borpendy/DSpi/3D Files/Plate/topcover.stl

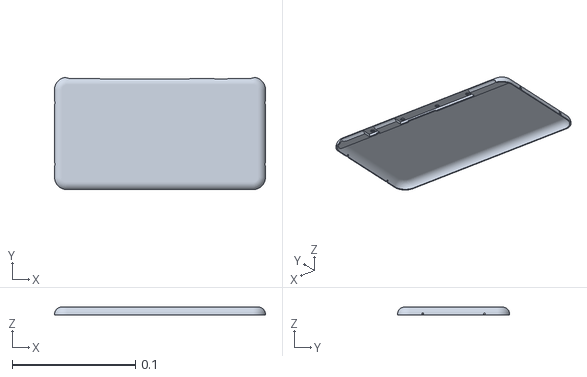
[picture p15: CAD file, 2025-08-22]
3D Files/Plate/topcover.stl
0.171 x 0.0909 x 0.0065
