borpendy/DSpi/3D Files/Buttons/Nosymbols/powerbutton.stl

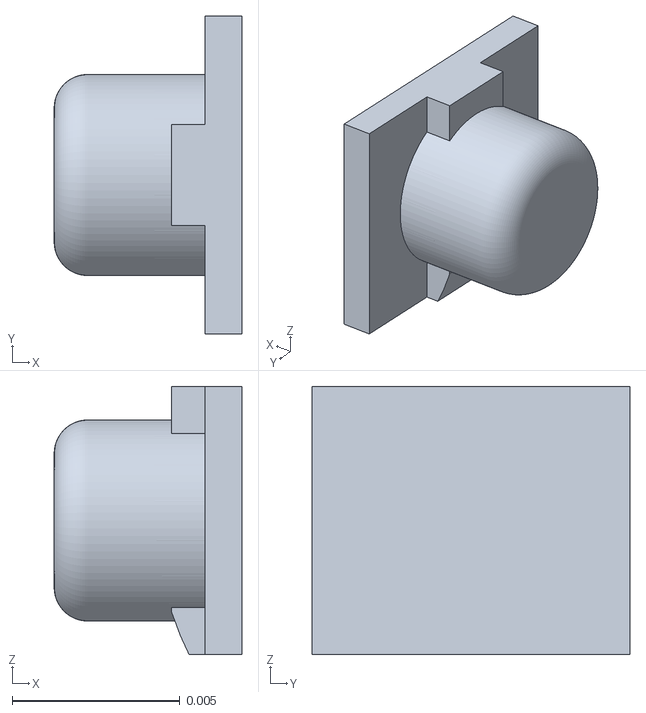
[picture p16: CAD file, 2025-08-22]
3D Files/Buttons/Nosymbols/powerbutton.stl
0.0056 x 0.00949 x 0.008
