borpendy/DSpi/3D Files/Buttons/Symbols/rt.stl

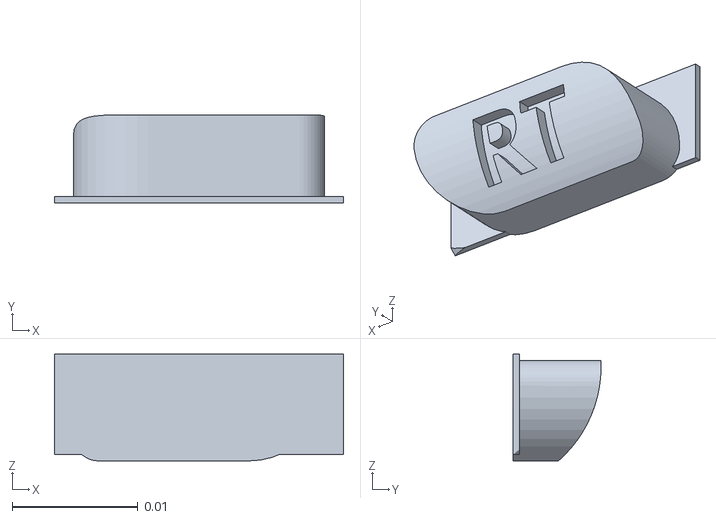
[picture p17: CAD file, 2025-08-22]
3D Files/Buttons/Symbols/rt.stl
0.023 x 0.00702 x 0.0085
