borpendy/DSpi/3D Files/Hinge/hinge-bottomleft.stl

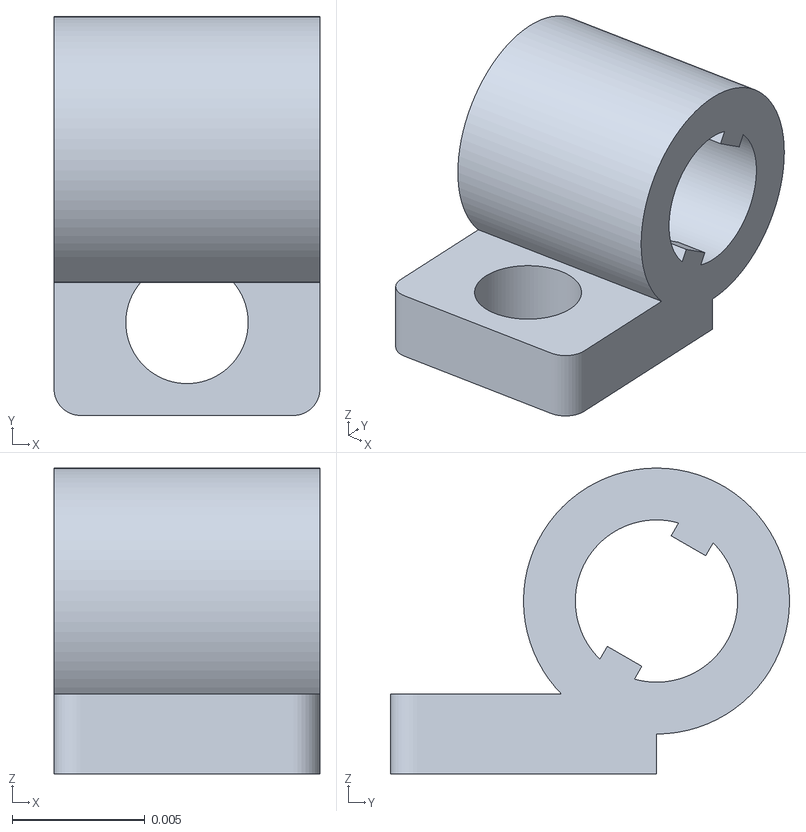
[picture p18: CAD file, 2025-08-22]
3D Files/Hinge/hinge-bottomleft.stl
0.01 x 0.015 x 0.0115
