borpendy/DSpi/3D Files/Misc/fanmount.stl

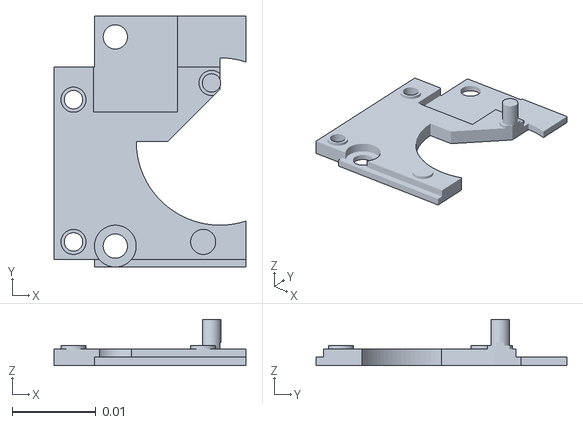
[picture p19: CAD file, 2025-08-22]
3D Files/Misc/fanmount.stl
0.0229 x 0.03 x 0.0055
