borpendy/DSpi/3D Files/Plate/lowerscreenmount-back.stl

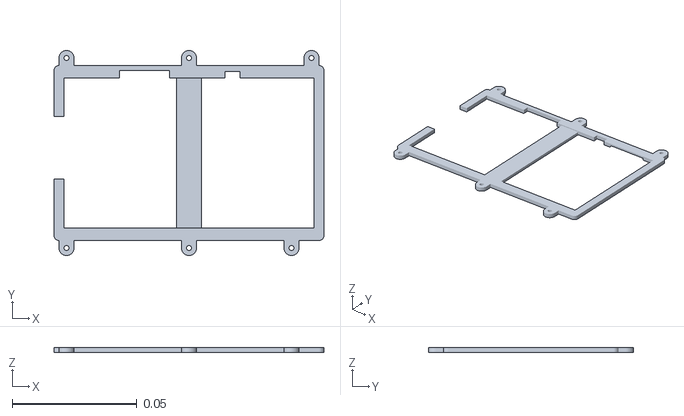
[picture p20: CAD file, 2025-08-22]
3D Files/Plate/lowerscreenmount-back.stl
0.108 x 0.082 x 0.002
