borpendy/DSpi/3D Files/Buttons/Symbols/rs.stl

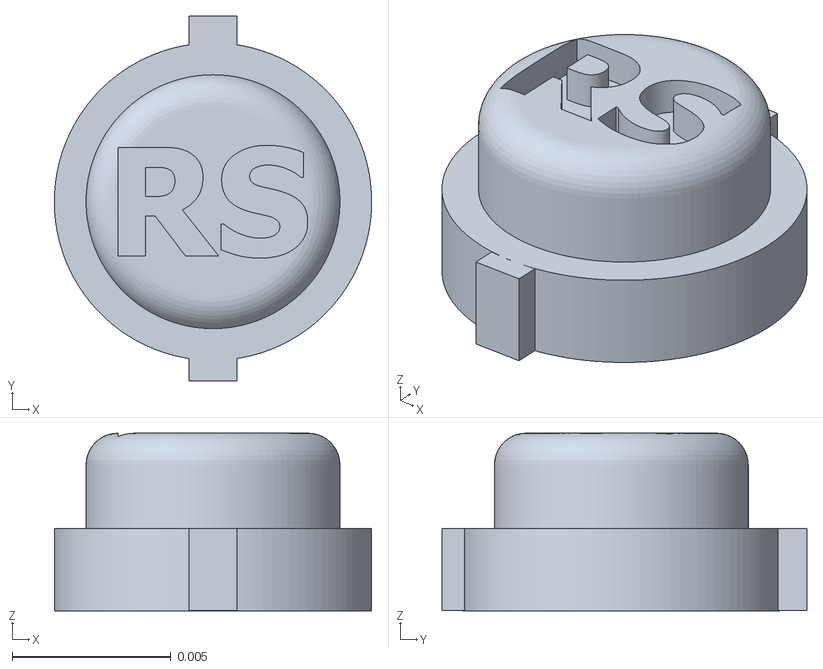
[picture p22: CAD file, 2025-08-22]
3D Files/Buttons/Symbols/rs.stl
0.01 x 0.0115 x 0.0056
