borpendy/DSpi/3D Files/Misc/batterymount.stl

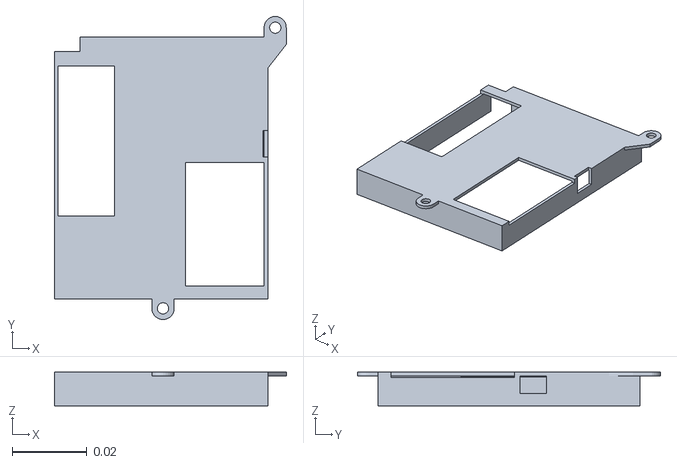
[picture p24: CAD file, 2025-08-22]
3D Files/Misc/batterymount.stl
0.062 x 0.081 x 0.009
