borpendy/DSpi/3D Files/Plate/lowerscreenmount.stl

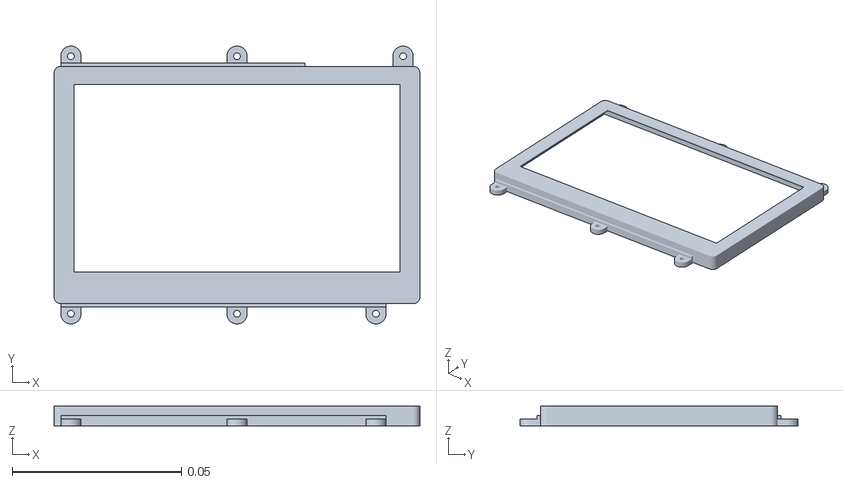
[picture p25: CAD file, 2025-08-22]
3D Files/Plate/lowerscreenmount.stl
0.108 x 0.082 x 0.0058
