borpendy/DSpi/3D Files/Hinge/topcover-l.stl

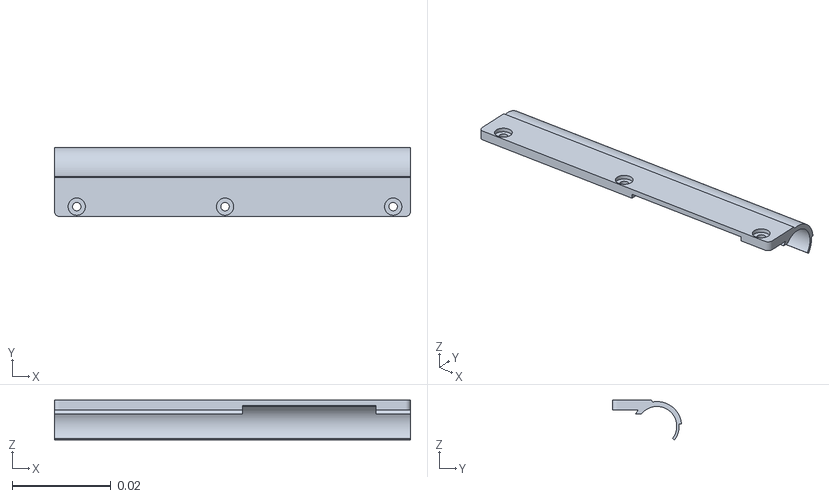
[picture p27: CAD file, 2025-08-22]
3D Files/Hinge/topcover-l.stl
0.072 x 0.014 x 0.00807
