borpendy/DSpi/3D Files/Plate/bottomplate.stl

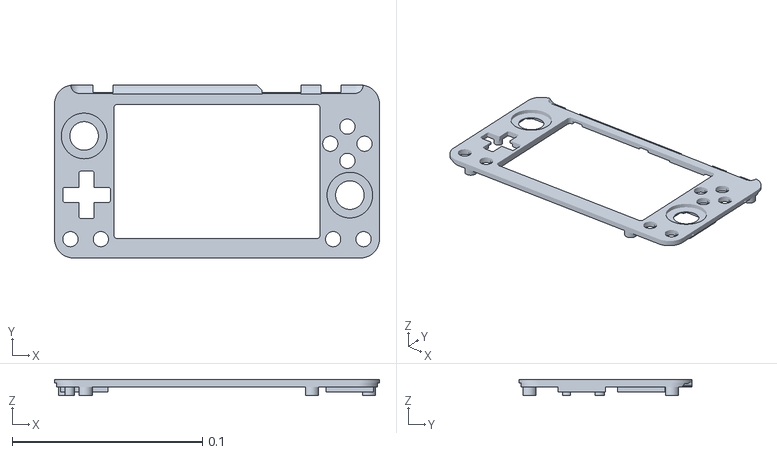
[picture p28: CAD file, 2025-08-22]
3D Files/Plate/bottomplate.stl
0.171 x 0.091 x 0.0085
