borpendy/DSpi/3D Files/Buttons/Symbols/x.stl

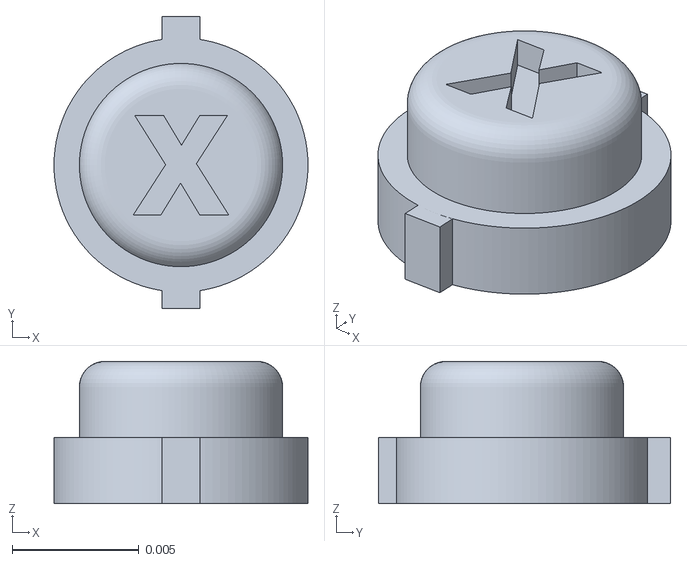
[picture p29: CAD file, 2025-08-22]
3D Files/Buttons/Symbols/x.stl
0.01 x 0.0115 x 0.0056
