borpendy/DSpi/3D Files/Hinge/hinge-topleft.stl

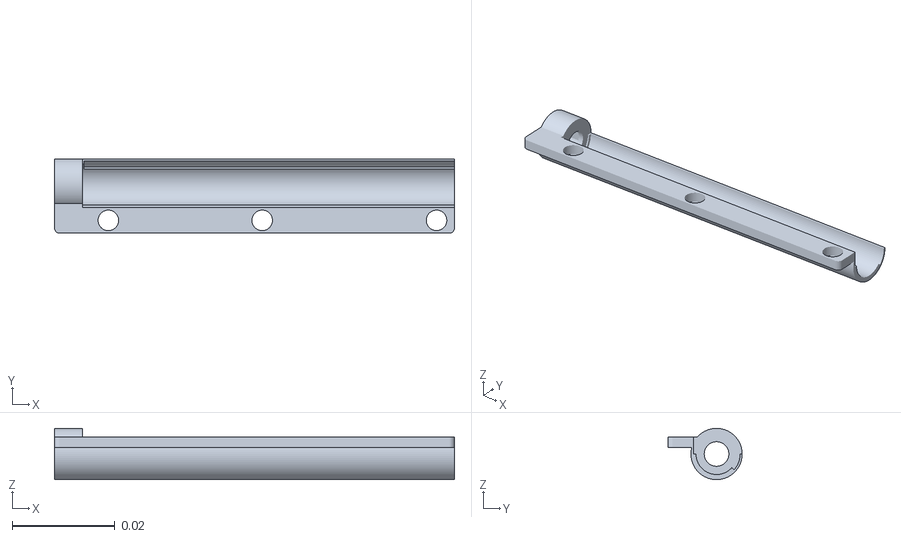
[picture p30: CAD file, 2025-08-22]
3D Files/Hinge/hinge-topleft.stl
0.078 x 0.0145 x 0.01
