borpendy/DSpi/3D Files/Hinge/hinge-topright.stl

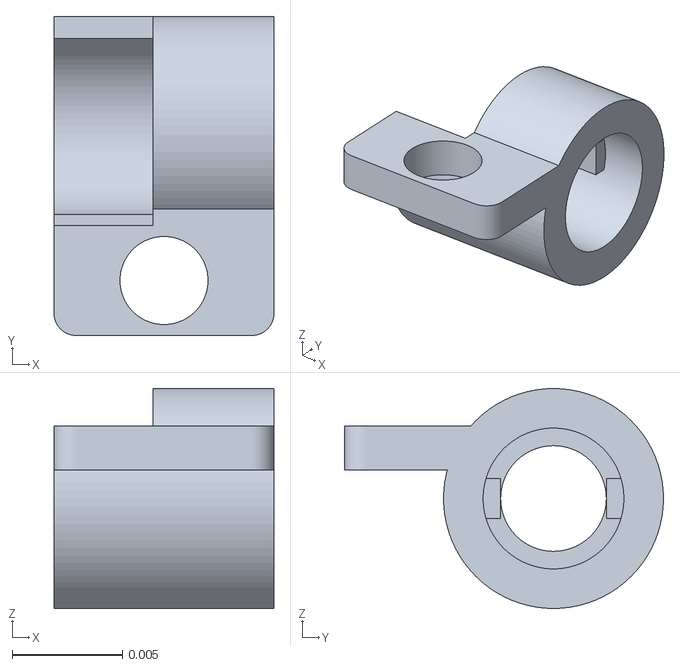
[picture p31: CAD file, 2025-08-22]
3D Files/Hinge/hinge-topright.stl
0.01 x 0.0145 x 0.01
