borpendy/DSpi/3D Files/Buttons/Symbols/lt.stl

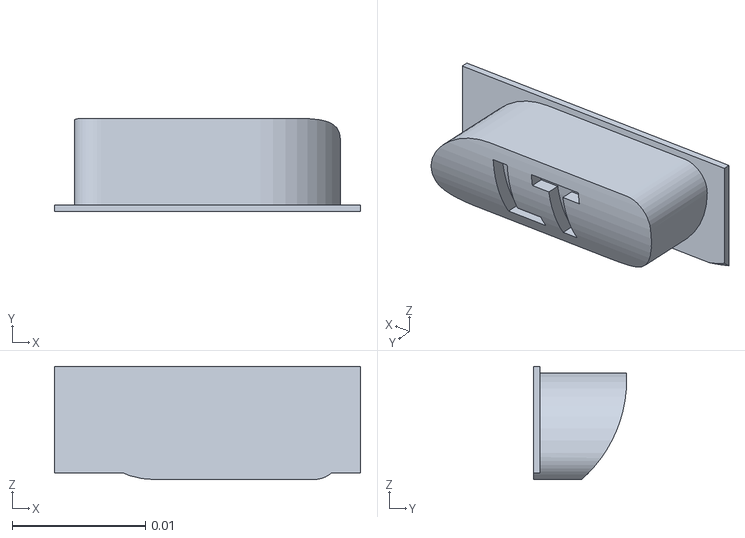
[picture p32: CAD file, 2025-08-22]
3D Files/Buttons/Symbols/lt.stl
0.023 x 0.00702 x 0.0085
