borpendy/DSpi/3D Files/Buttons/Symbols/s1.stl

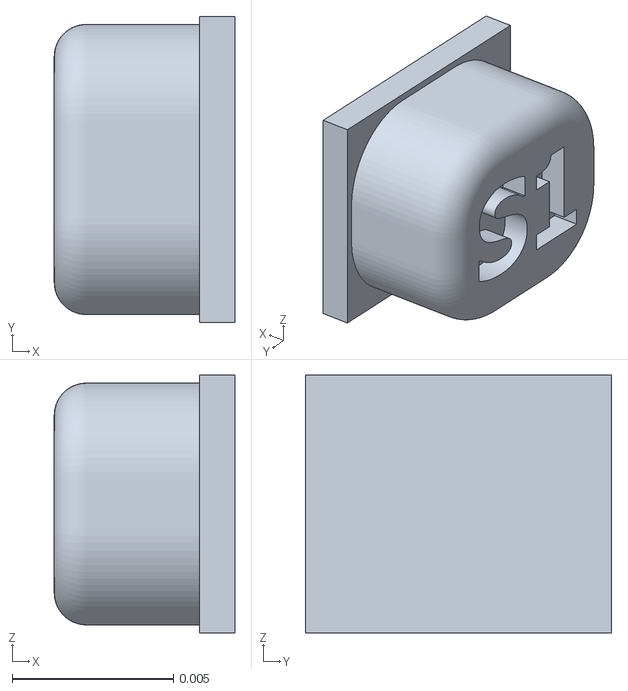
[picture p33: CAD file, 2025-08-22]
3D Files/Buttons/Symbols/s1.stl
0.0056 x 0.00949 x 0.008
