borpendy/DSpi/3D Files/Buttons/Symbols/lb.stl

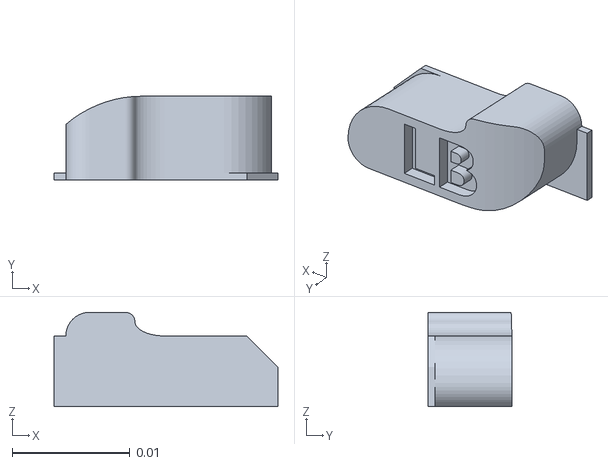
[picture p34: CAD file, 2025-08-22]
3D Files/Buttons/Symbols/lb.stl
0.019 x 0.0071 x 0.008
