borpendy/DSpi/3D Files/Buttons/Symbols/dpad.stl

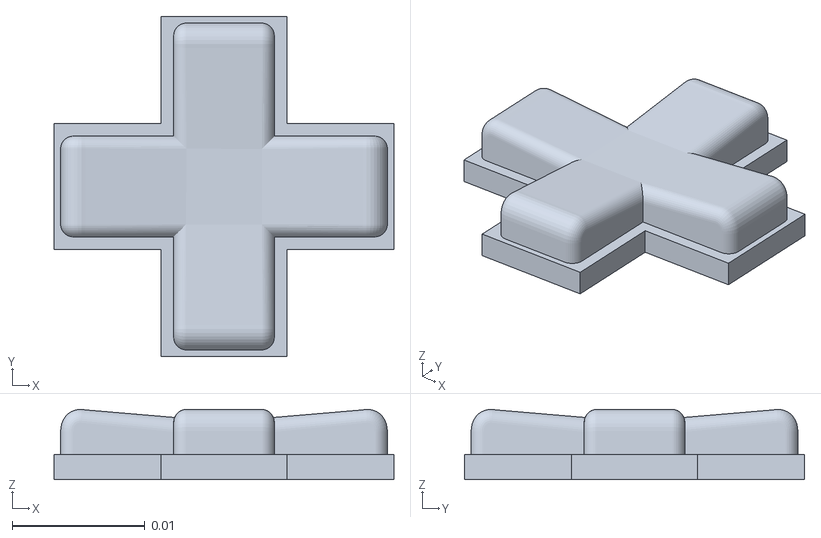
[picture p35: CAD file, 2025-08-22]
3D Files/Buttons/Symbols/dpad.stl
0.0256 x 0.0257 x 0.0053
